jordankooyman/3D-Printed-DIY-Joystick/3D Files/STL/Handle/5-way button spacer.stl

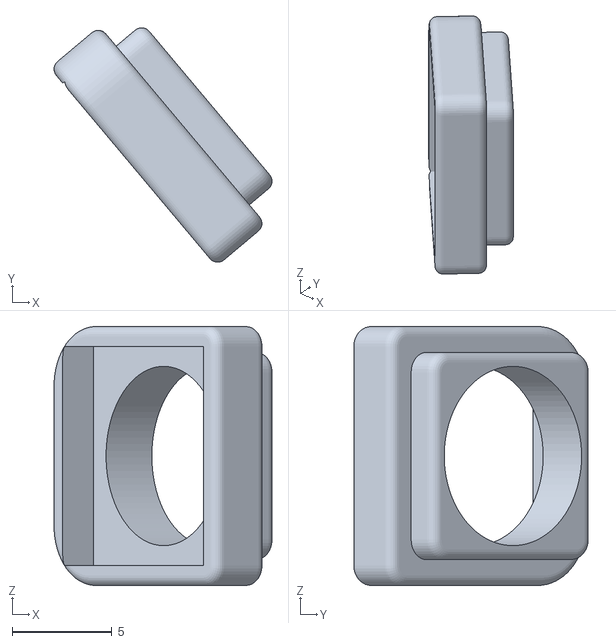
[picture p18: CAD file, 2021-07-30]
3D Files/STL/Handle/5-way button spacer.stl
10.9 x 11.8 x 13.0
