jordankooyman/3D-Printed-DIY-Joystick/3D Files/STL/Throttle Add-On 2.0/Imported Parts - Sample Only/40T 2.75mm MXL Pulley for Pot.stl

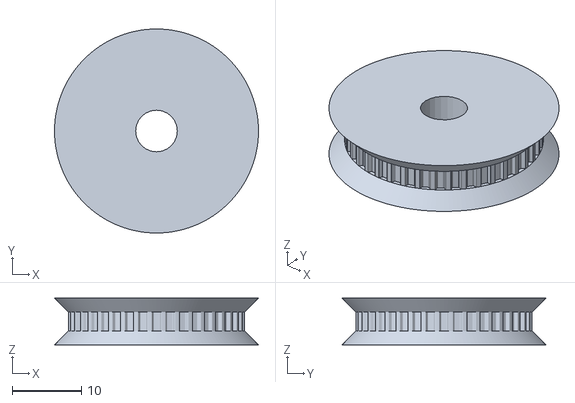
[picture p20: CAD file, 2021-07-30]
3D Files/STL/Throttle Add-On 2.0/Imported Parts - Sample Only/40T 2.75mm MXL Pulley for Pot.stl
29.4 x 29.4 x 6.75
