jordankooyman/3D-Printed-DIY-Joystick/3D Files/STL/Base - Version D/cable cap.stl

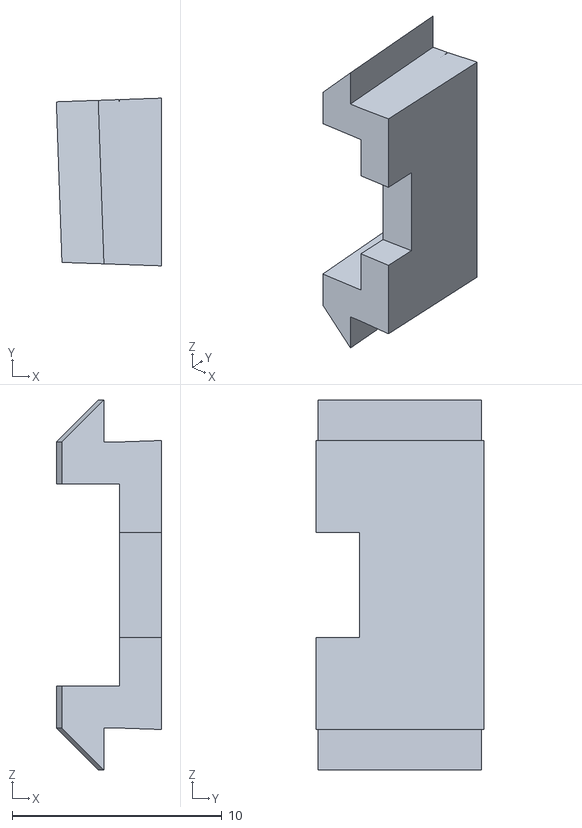
[picture p21: CAD file, 2021-07-30]
3D Files/STL/Base - Version D/cable cap.stl
5.02 x 8.00 x 17.6
