jordankooyman/3D-Printed-DIY-Joystick/3D Files/STL/Chair Mount - For Reference Only/Left Bottom Front Clamp.stl

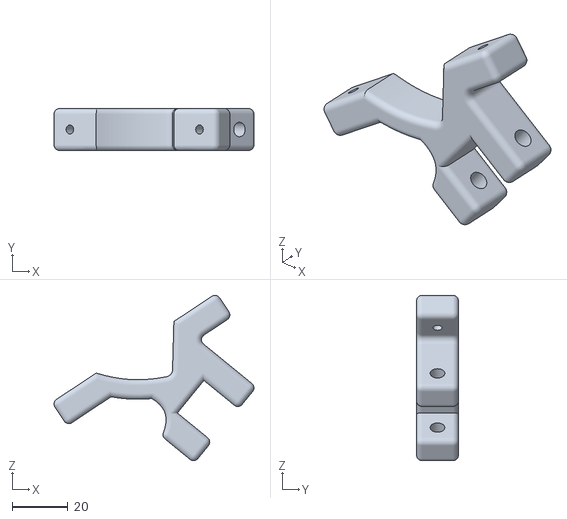
[picture p22: CAD file, 2021-07-30]
3D Files/STL/Chair Mount - For Reference Only/Left Bottom Front Clamp.stl
71.5 x 15.0 x 59.1
