jordankooyman/3D-Printed-DIY-Joystick/3D Files/STL/Handle/Stadium Hat.stl

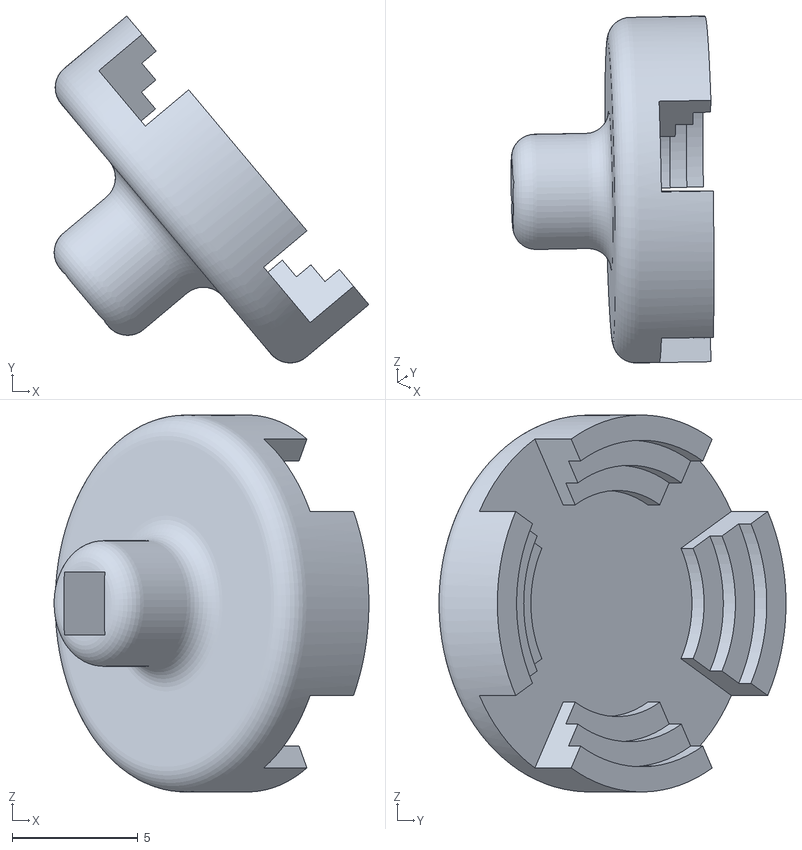
[picture p23: CAD file, 2021-07-30]
3D Files/STL/Handle/Stadium Hat.stl
12.5 x 13.8 x 15.0
