jordankooyman/3D-Printed-DIY-Joystick/3D Files/STL/Throttle Add-On 2.0/Belt Pin Spacer.stl

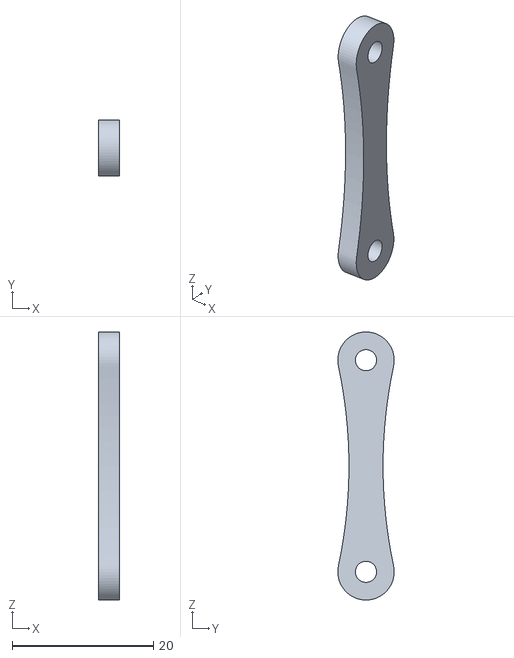
[picture p24: CAD file, 2021-07-30]
3D Files/STL/Throttle Add-On 2.0/Belt Pin Spacer.stl
3.00 x 8.00 x 38.0
