jordankooyman/3D-Printed-DIY-Joystick/3D Files/STL/Throttle Add-On 2.0/Imported Parts - Sample Only/20T 2.75mm MXL Pulley.stl

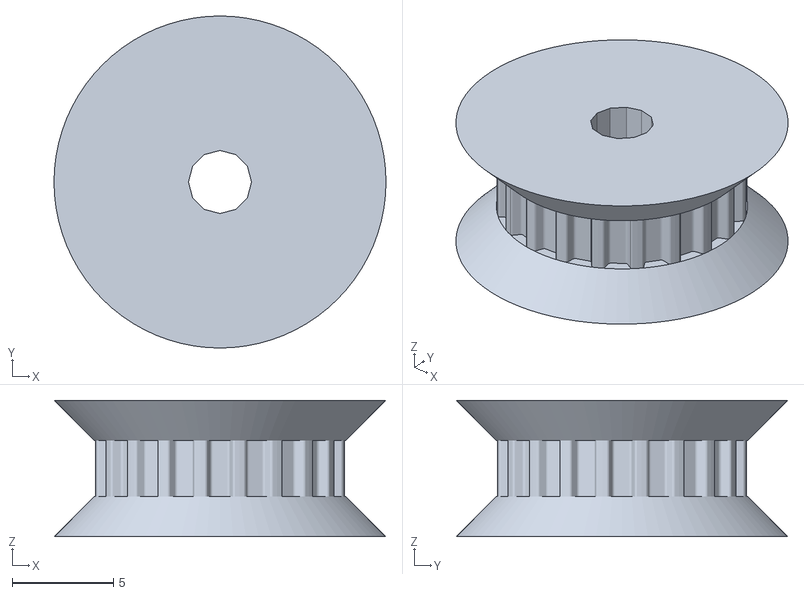
[picture p25: CAD file, 2021-07-30]
3D Files/STL/Throttle Add-On 2.0/Imported Parts - Sample Only/20T 2.75mm MXL Pulley.stl
16.4 x 16.4 x 6.75
