jordankooyman/3D-Printed-DIY-Joystick/3D Files/STL/Base - Version D/Yaw Spring 2.stl

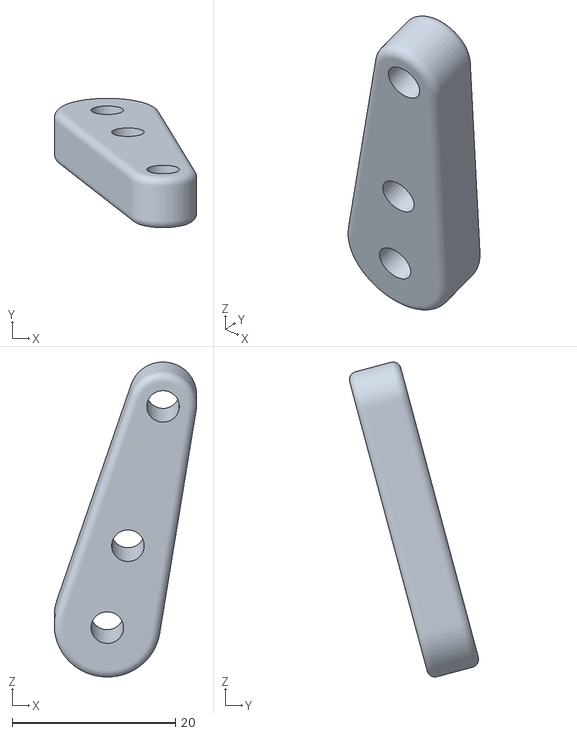
[picture p26: CAD file, 2021-07-30]
3D Files/STL/Base - Version D/Yaw Spring 2.stl
17.4 x 15.8 x 38.6
