jordankooyman/3D-Printed-DIY-Joystick/3D Files/STL/Chair Mount - For Reference Only/Long Support Clamp Base.stl

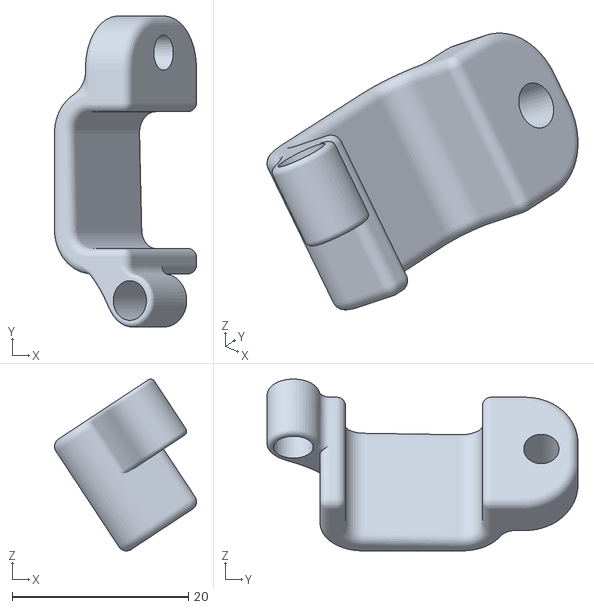
[picture p27: CAD file, 2021-07-30]
3D Files/STL/Chair Mount - For Reference Only/Long Support Clamp Base.stl
16.1 x 35.3 x 19.5
