jordankooyman/3D-Printed-DIY-Joystick/3D Files/STL/Handle/Trim Hat.stl

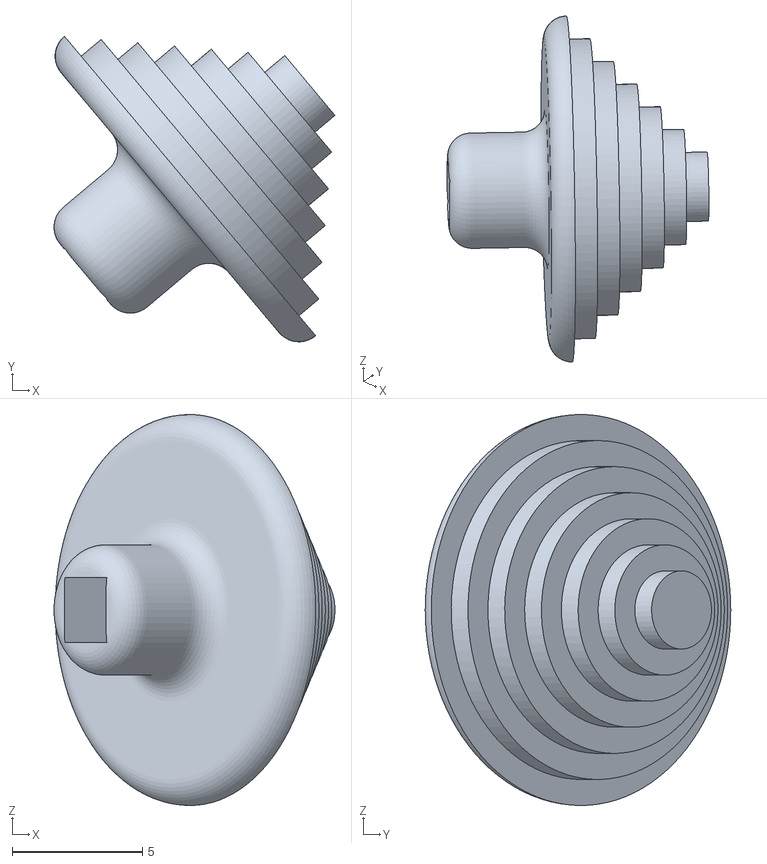
[picture p28: CAD file, 2021-07-30]
3D Files/STL/Handle/Trim Hat.stl
10.8 x 11.7 x 15.0
