jordankooyman/3D-Printed-DIY-Joystick/3D Files/STL/Throttle Add-On 2.0/Cover 2.stl

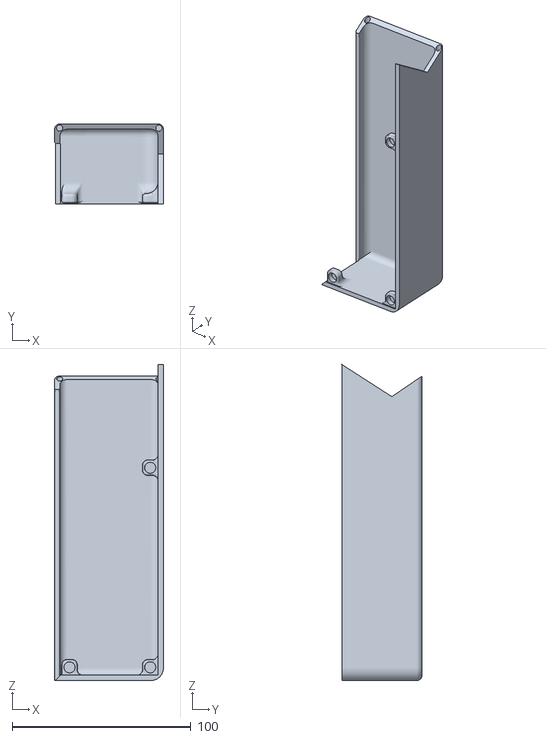
[picture p29: CAD file, 2021-07-30]
3D Files/STL/Throttle Add-On 2.0/Cover 2.stl
61.0 x 45.0 x 177.0
