jordankooyman/3D-Printed-DIY-Joystick/3D Files/STL/Base - Version D/axis_for_ver_D v3.stl

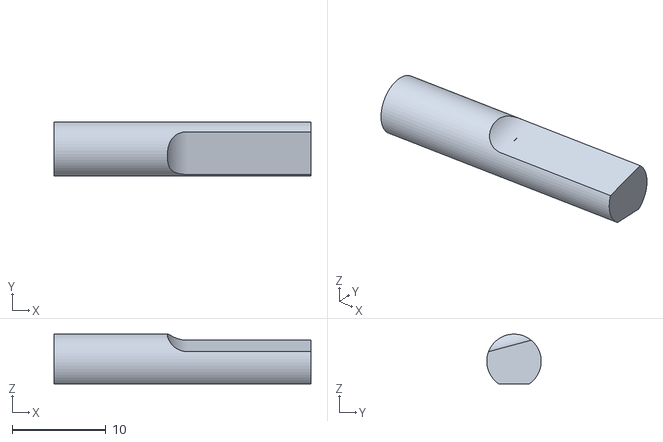
[picture p30: CAD file, 2021-07-30]
3D Files/STL/Base - Version D/axis_for_ver_D v3.stl
27.4 x 5.79 x 5.29
