jordankooyman/3D-Printed-DIY-Joystick/3D Files/STL/Chair Mount - For Reference Only/Long Support Arm Bottom.stl

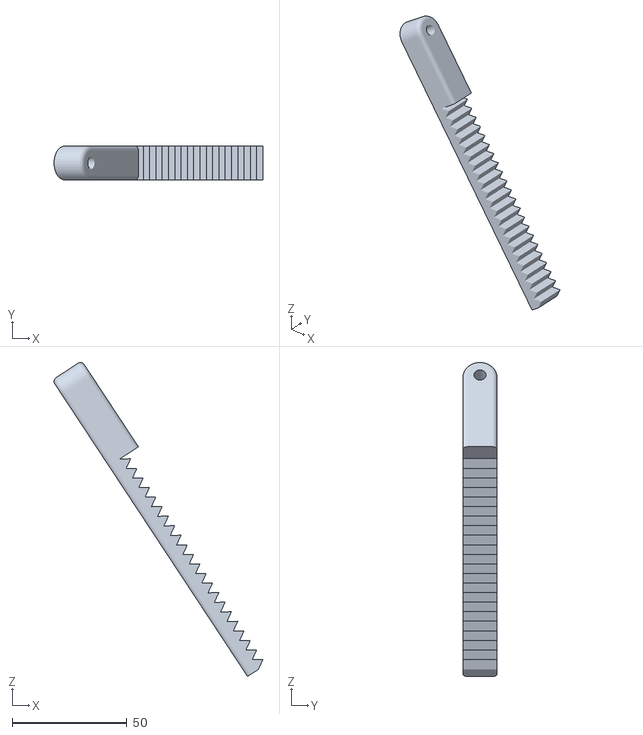
[picture p31: CAD file, 2021-07-30]
3D Files/STL/Chair Mount - For Reference Only/Long Support Arm Bottom.stl
91.2 x 15.0 x 137.1
