jordankooyman/3D-Printed-DIY-Joystick/3D Files/STL/Handle/joystick_grip_right_side v2.stl

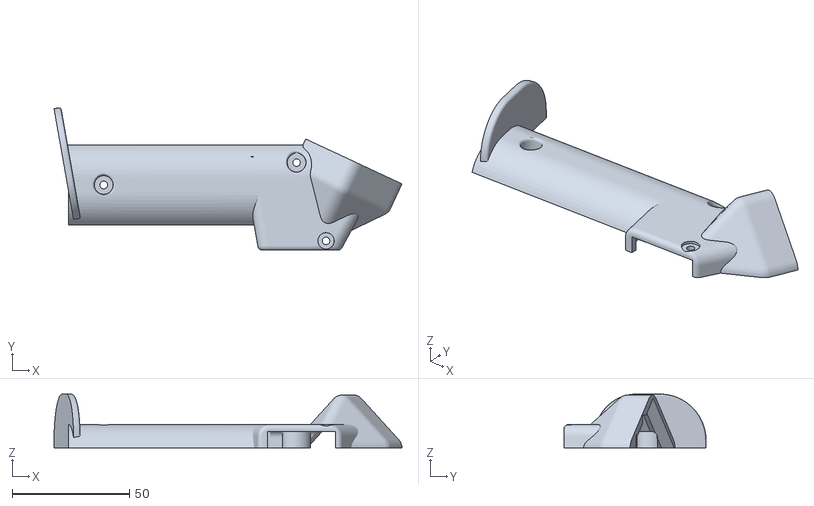
[picture p32: CAD file, 2021-07-30]
3D Files/STL/Handle/joystick_grip_right_side v2.stl
148.5 x 60.8 x 23.0
