jordankooyman/3D-Printed-DIY-Joystick/3D Files/STL/Throttle Add-On 2.0/Mount.stl

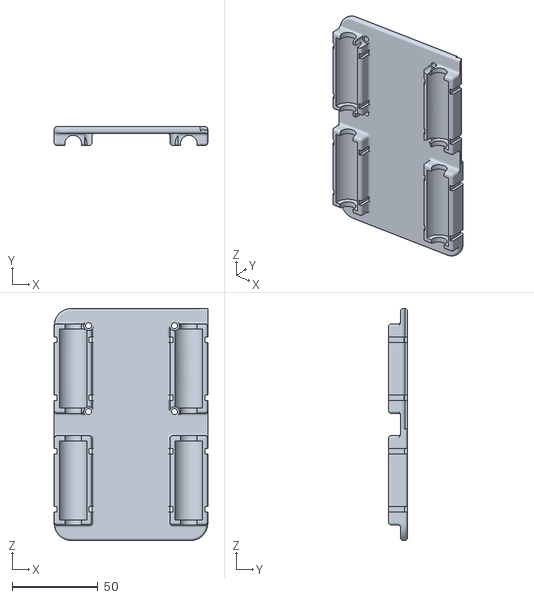
[picture p33: CAD file, 2021-07-30]
3D Files/STL/Throttle Add-On 2.0/Mount.stl
89.4 x 11.0 x 135.0
