jordankooyman/3D-Printed-DIY-Joystick/3D Files/STL/Base - Version D/hinge_cam.stl

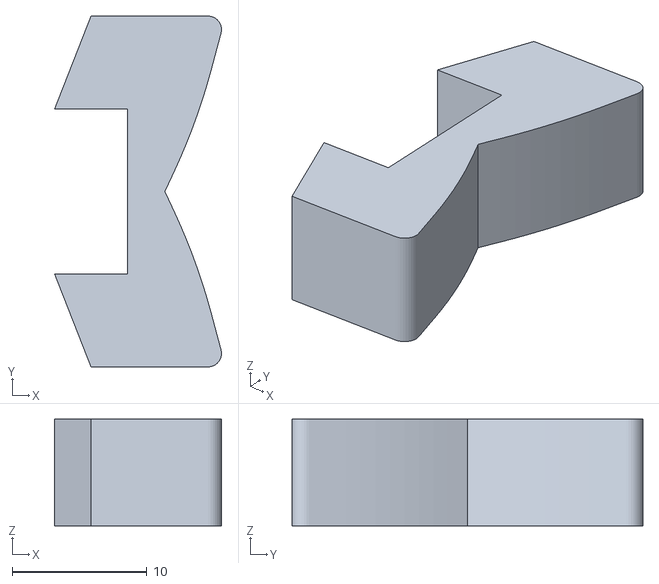
[picture p34: CAD file, 2021-07-30]
3D Files/STL/Base - Version D/hinge_cam.stl
12.4 x 26.0 x 7.90
