jordankooyman/3D-Printed-DIY-Joystick/3D Files/STL/Chair Mount - For Reference Only/Left Top Front Clamp.stl

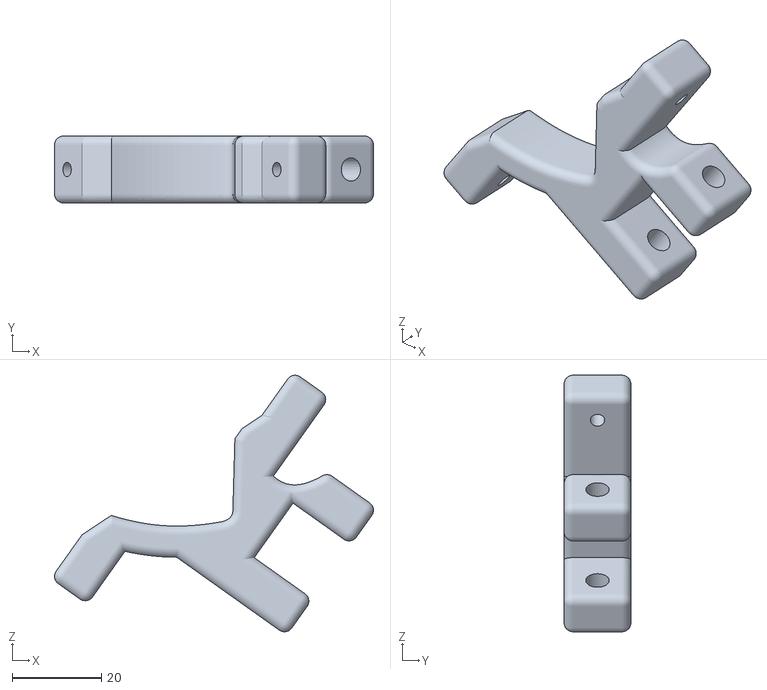
[picture p35: CAD file, 2021-07-30]
3D Files/STL/Chair Mount - For Reference Only/Left Top Front Clamp.stl
71.5 x 15.0 x 57.5
