jordankooyman/3D-Printed-DIY-Joystick/3D Files/STL/Handle/Face Plate.stl

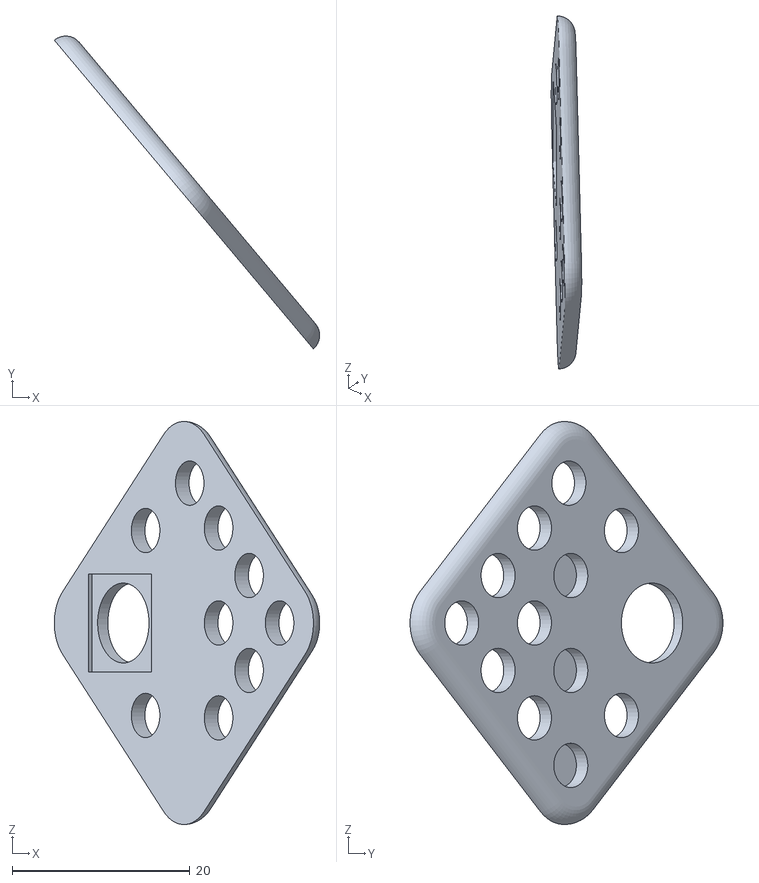
[picture p36: CAD file, 2021-07-30]
3D Files/STL/Handle/Face Plate.stl
29.8 x 35.2 x 45.3
