jordankooyman/3D-Printed-DIY-Joystick/3D Files/STL/Throttle Add-On 2.0/Adjustable Pot Mount.stl

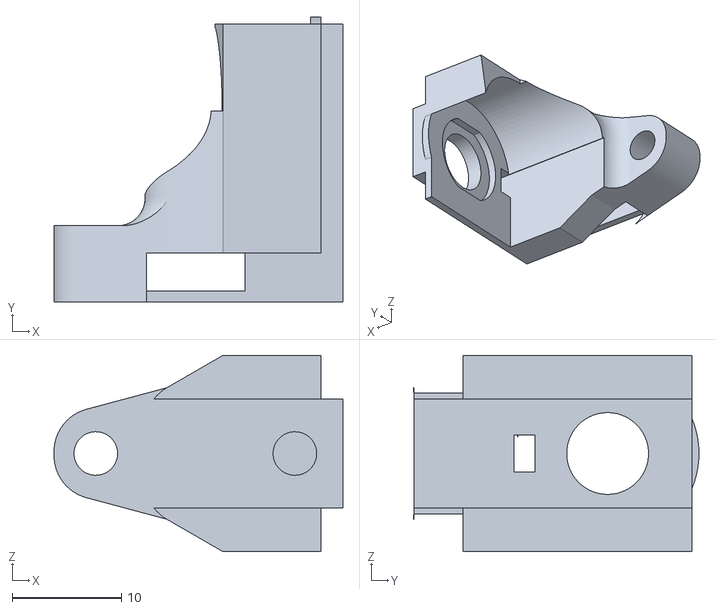
[picture p37: CAD file, 2021-07-30]
3D Files/STL/Throttle Add-On 2.0/Adjustable Pot Mount.stl
26.5 x 26.1 x 18.0
