jordankooyman/3D-Printed-DIY-Joystick/3D Files/STL/Base - Version D/trim knob.stl

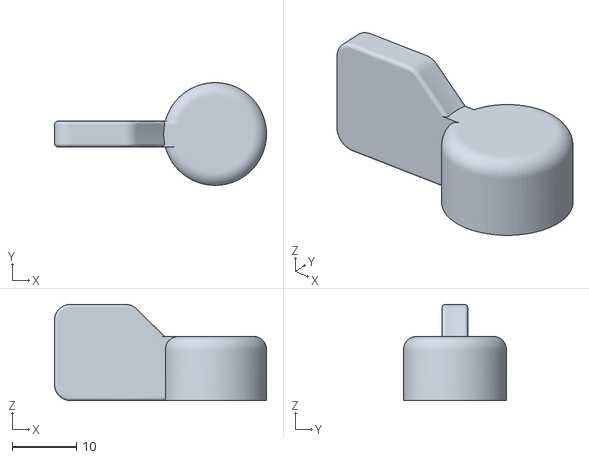
[picture p38: CAD file, 2021-07-30]
3D Files/STL/Base - Version D/trim knob.stl
33.0 x 16.0 x 15.0
