jordankooyman/3D-Printed-DIY-Joystick/3D Files/STL/Chair Mount - For Reference Only/Short Support Arm 2.stl

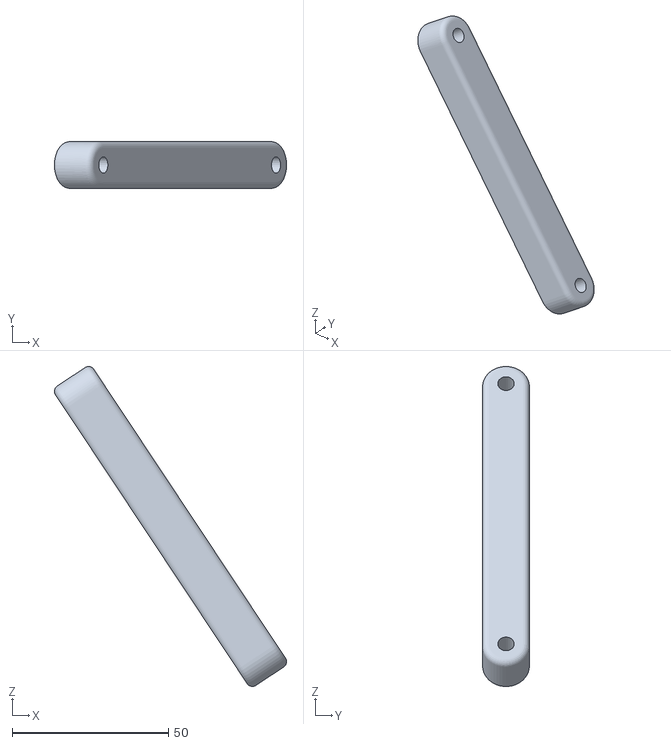
[picture p39: CAD file, 2021-07-30]
3D Files/STL/Chair Mount - For Reference Only/Short Support Arm 2.stl
74.3 x 15.0 x 102.4
