jordankooyman/3D-Printed-DIY-Joystick/3D Files/STL/Handle/joystick grip left side filled.3mf

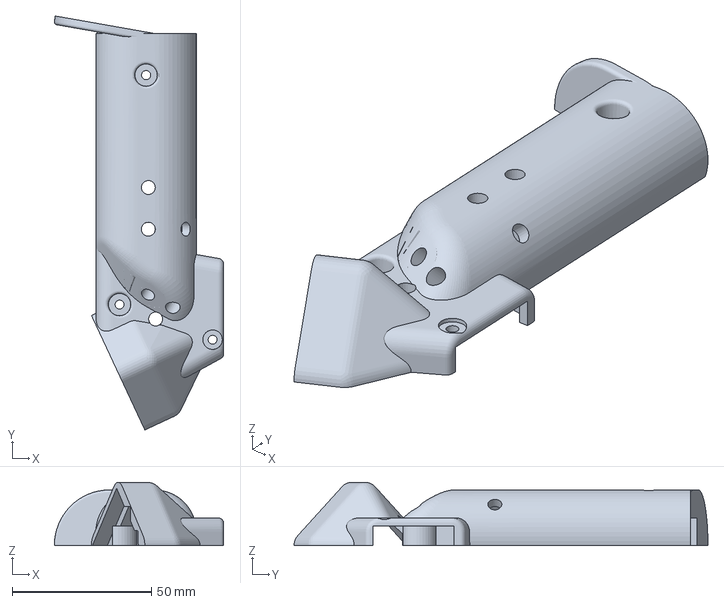
[picture p40: CAD file, 2021-07-30]
3D Files/STL/Handle/joystick grip left side filled.3mf
60.8 x 148.5 x 22.7 mm
