jordankooyman/3D-Printed-DIY-Joystick/3D Files/STL/Throttle Add-On 2.0/Mount Side.stl

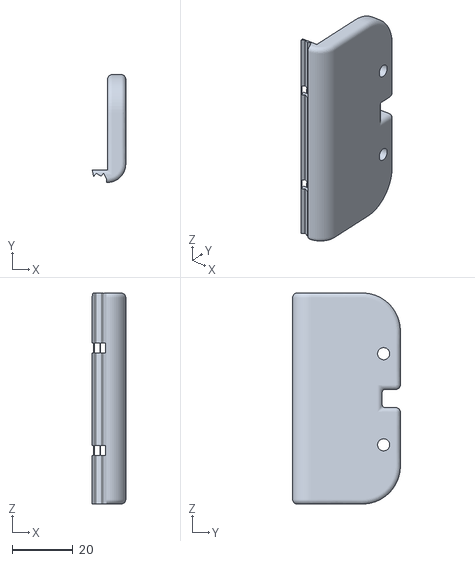
[picture p41: CAD file, 2021-07-30]
3D Files/STL/Throttle Add-On 2.0/Mount Side.stl
11.1 x 35.5 x 69.5
