jordankooyman/3D-Printed-DIY-Joystick/3D Files/STL/Base - Version D/Wire Storage Clip.stl

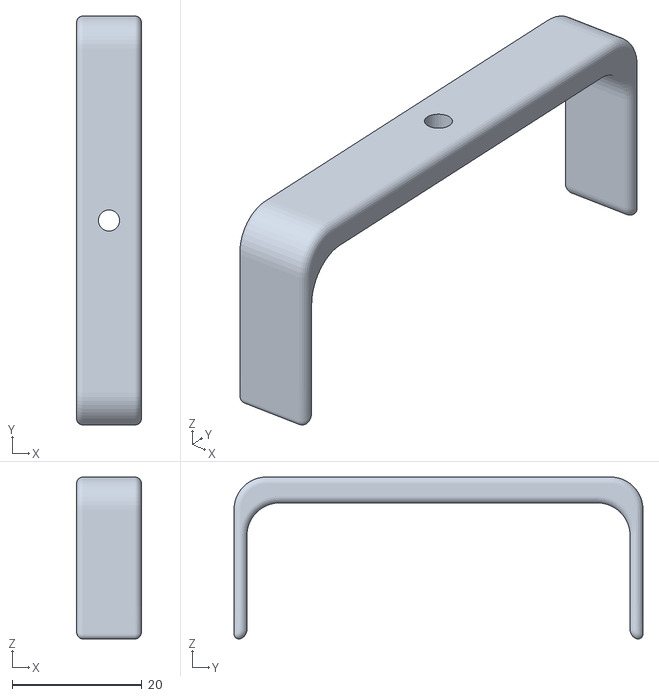
[picture p42: CAD file, 2021-07-30]
3D Files/STL/Base - Version D/Wire Storage Clip.stl
10.0 x 63.0 x 25.0
