jordankooyman/3D-Printed-DIY-Joystick/3D Files/STL/Chair Mount - For Reference Only/Left Clamp Back Bottom.stl

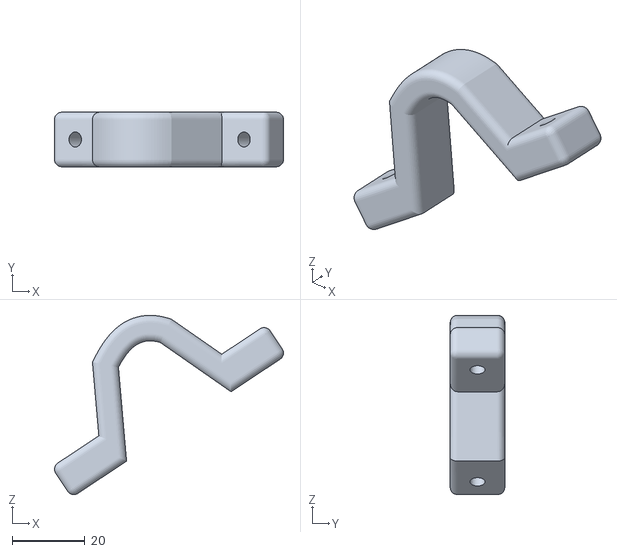
[picture p43: CAD file, 2021-07-30]
3D Files/STL/Chair Mount - For Reference Only/Left Clamp Back Bottom.stl
62.9 x 15.0 x 49.2
