jordankooyman/3D-Printed-DIY-Joystick/3D Files/STL/Handle/trigger.stl

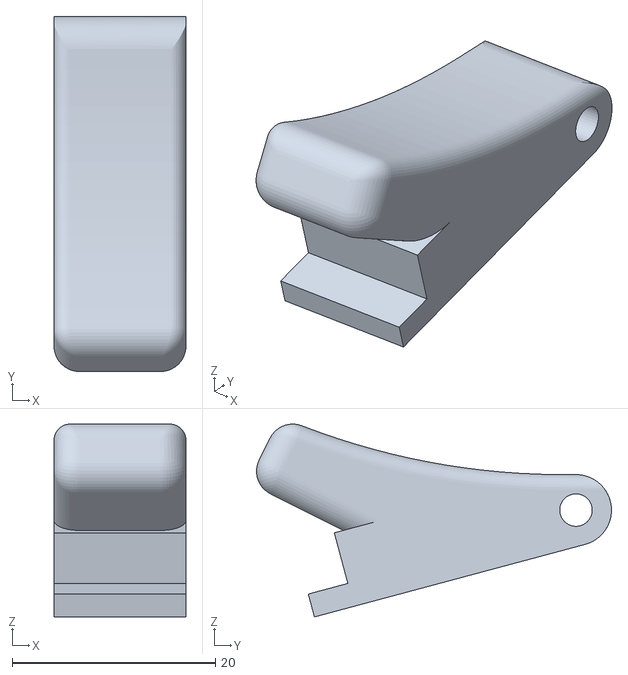
[picture p44: CAD file, 2021-07-30]
3D Files/STL/Handle/trigger.stl
13.0 x 35.0 x 19.0
