jordankooyman/3D-Printed-DIY-Joystick/3D Files/STL/Throttle Add-On 2.0/Base 2.stl

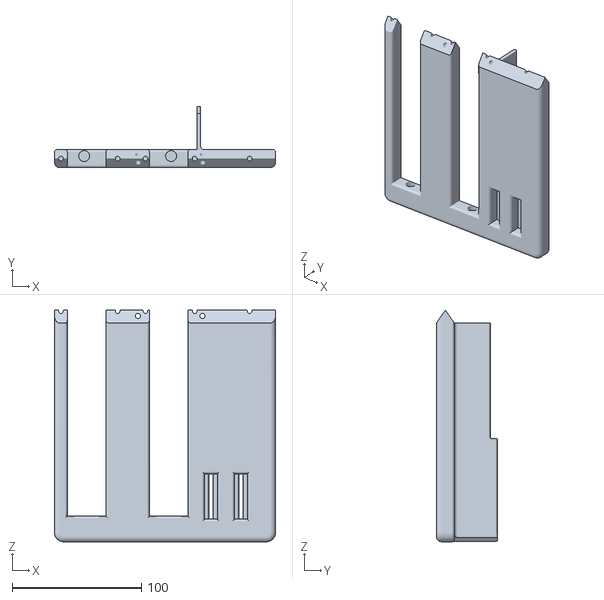
[picture p45: CAD file, 2021-07-30]
3D Files/STL/Throttle Add-On 2.0/Base 2.stl
171.2 x 47.5 x 179.5
