jordankooyman/3D-Printed-DIY-Joystick/3D Files/STL/Base - Version D/base_cover.stl

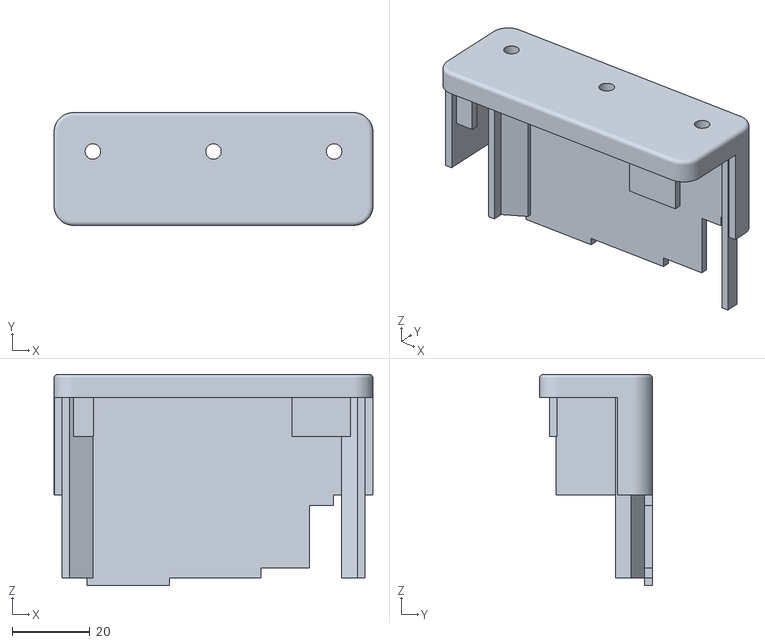
[picture p46: CAD file, 2021-07-30]
3D Files/STL/Base - Version D/base_cover.stl
82.0 x 29.0 x 54.3
