jordankooyman/3D-Printed-DIY-Joystick/3D Files/STL/Chair Mount - For Reference Only/M5 Cap.stl

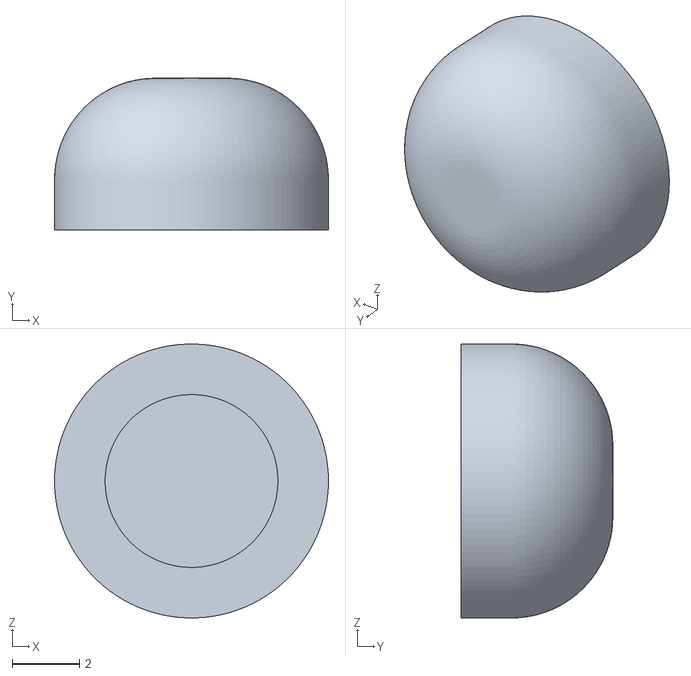
[picture p47: CAD file, 2021-07-30]
3D Files/STL/Chair Mount - For Reference Only/M5 Cap.stl
8.12 x 4.50 x 8.12
