jordankooyman/3D-Printed-DIY-Joystick/3D Files/STL/Handle/joystick_grip_left_side v2.stl

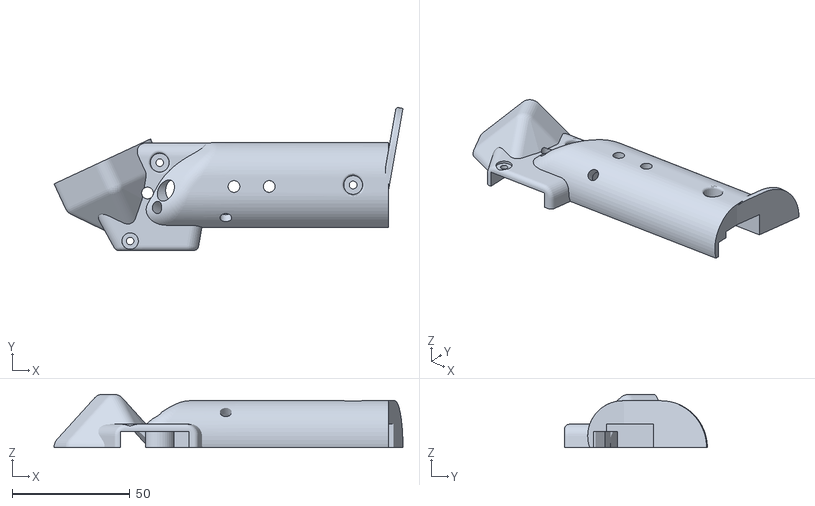
[picture p48: CAD file, 2021-07-30]
3D Files/STL/Handle/joystick_grip_left_side v2.stl
148.5 x 60.8 x 22.7
