jordankooyman/3D-Printed-DIY-Joystick/3D Files/STL/Base - Version D/M4 Bearing Spacer.stl

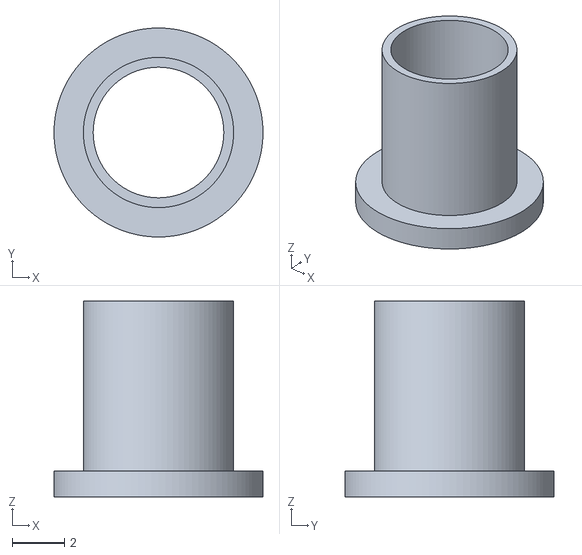
[picture p50: CAD file, 2021-07-30]
3D Files/STL/Base - Version D/M4 Bearing Spacer.stl
8.00 x 8.00 x 7.50
