jordankooyman/3D-Printed-DIY-Joystick/3D Files/STL/Handle/Button Cap Body.stl

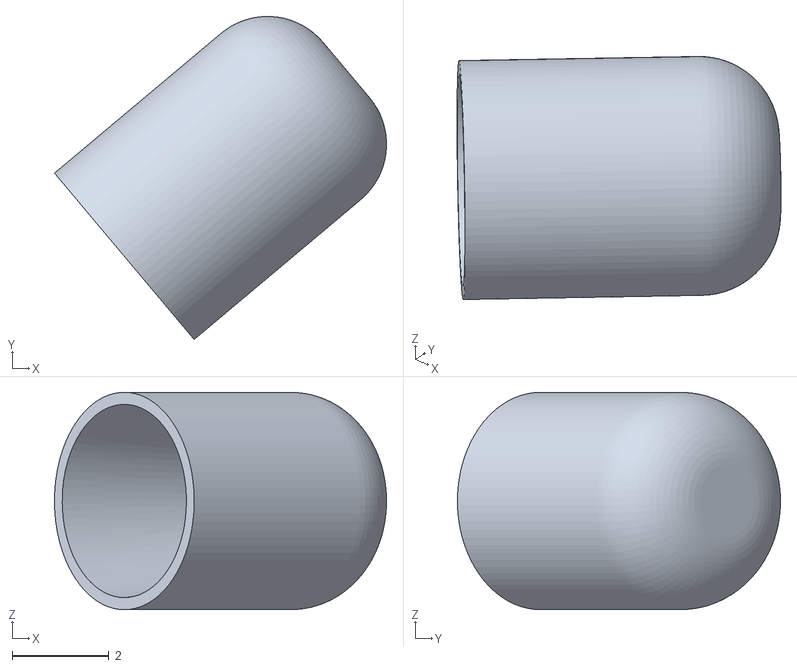
[picture p51: CAD file, 2021-07-30]
3D Files/STL/Handle/Button Cap Body.stl
6.87 x 6.69 x 4.50
