jordankooyman/3D-Printed-DIY-Joystick/3D Files/STL/Throttle Add-On 2.0/Idler Axle.stl

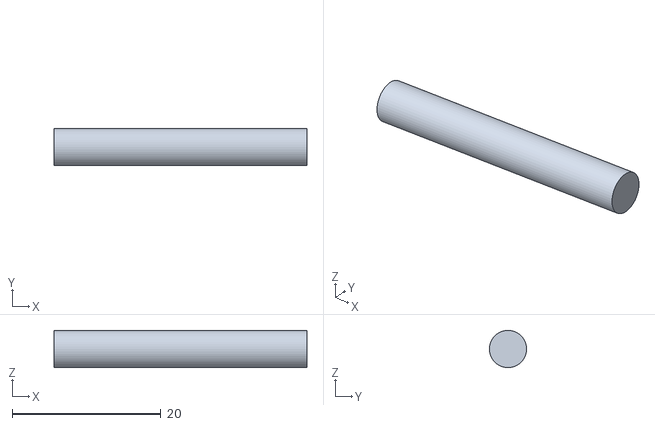
[picture p52: CAD file, 2021-07-30]
3D Files/STL/Throttle Add-On 2.0/Idler Axle.stl
34.0 x 5.00 x 5.00
