jordankooyman/3D-Printed-DIY-Joystick/3D Files/STL/Base - Version D/Bottom.stl

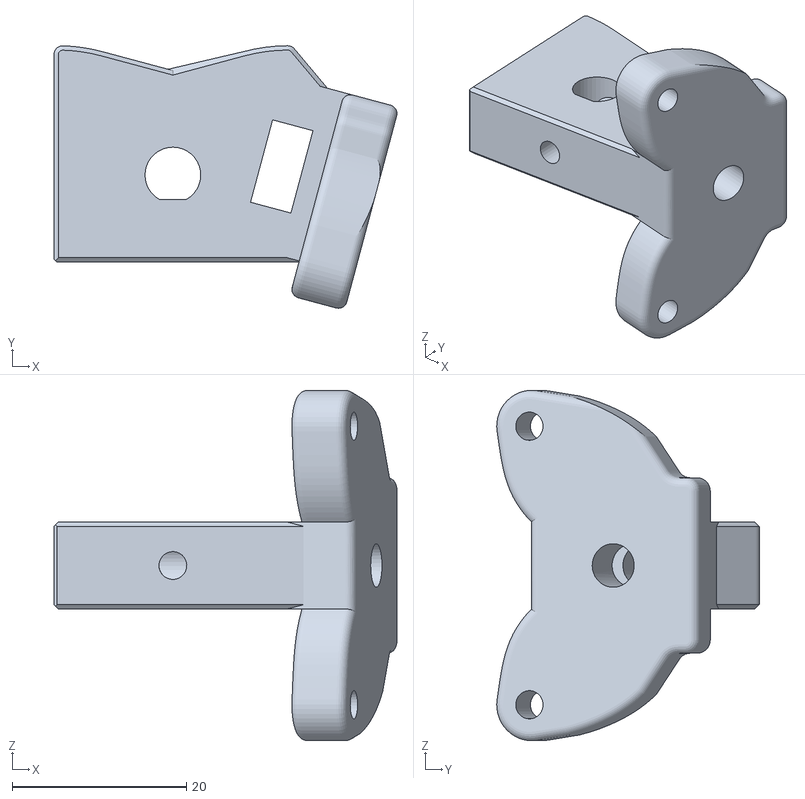
[picture p53: CAD file, 2021-07-30]
3D Files/STL/Base - Version D/Bottom.stl
39.4 x 30.2 x 40.2
