jordankooyman/3D-Printed-DIY-Joystick/3D Files/STL/Chair Mount - For Reference Only/Right Clamp Back Bottom.stl

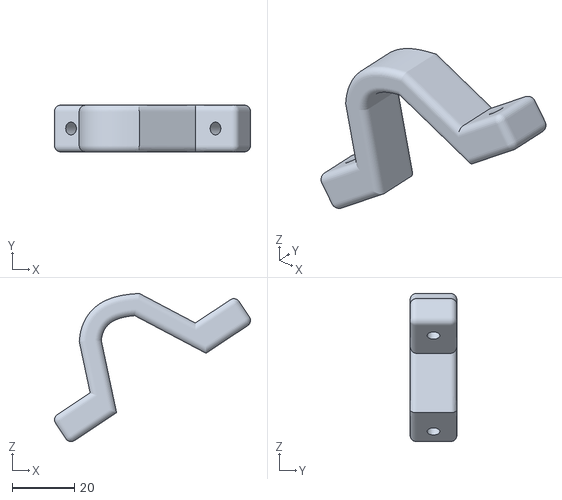
[picture p54: CAD file, 2021-07-30]
3D Files/STL/Chair Mount - For Reference Only/Right Clamp Back Bottom.stl
62.9 x 15.0 x 47.5
