jordankooyman/3D-Printed-DIY-Joystick/3D Files/STL/Base - Version D/cam_arm.stl

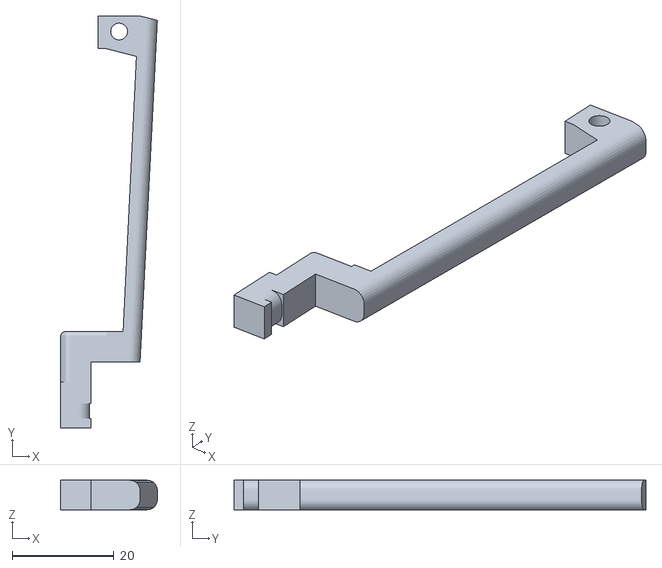
[picture p55: CAD file, 2021-07-30]
3D Files/STL/Base - Version D/cam_arm.stl
19.0 x 81.0 x 5.80
