jordankooyman/3D-Printed-DIY-Joystick/3D Files/STL/Chair Mount - For Reference Only/Short Support Arm.stl

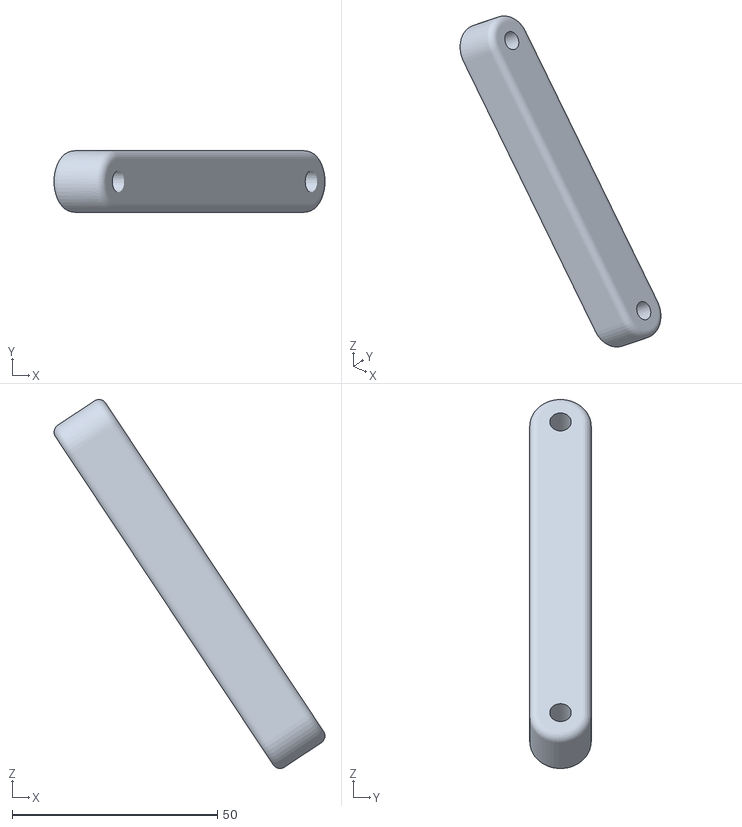
[picture p56: CAD file, 2021-07-30]
3D Files/STL/Chair Mount - For Reference Only/Short Support Arm.stl
66.0 x 15.0 x 89.9
