jordankooyman/3D-Printed-DIY-Joystick/3D Files/STL/Base - Version D/Mount Base.stl

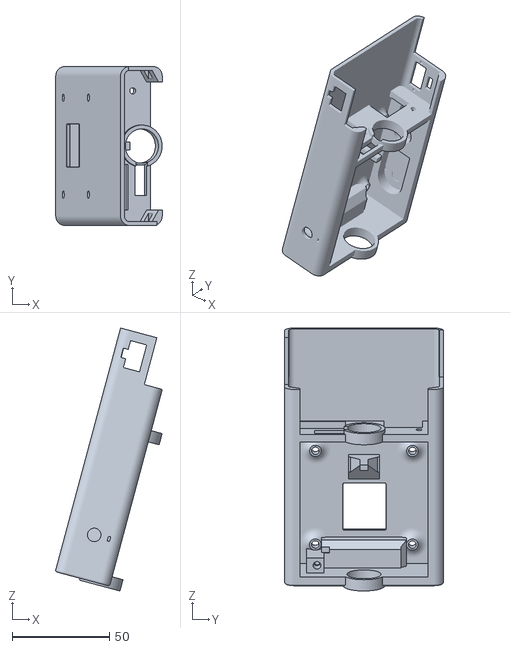
[picture p57: CAD file, 2021-07-30]
3D Files/STL/Base - Version D/Mount Base.stl
55.0 x 82.0 x 135.5
