jordankooyman/3D-Printed-DIY-Joystick/3D Files/STL/Chair Mount - For Reference Only/Right Bottom Front Clamp.stl

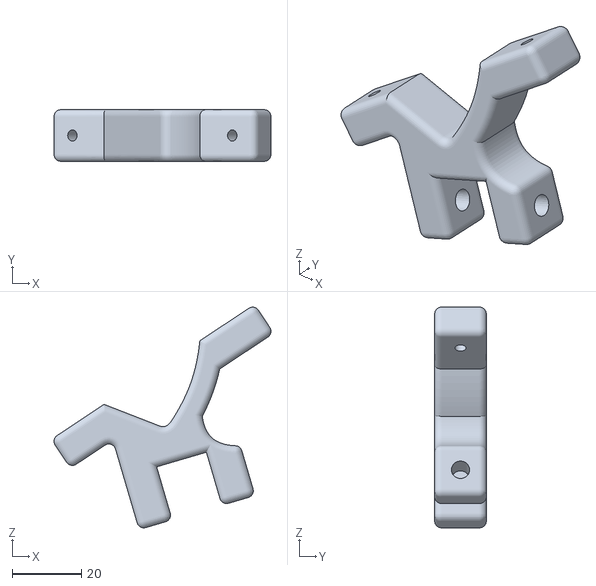
[picture p58: CAD file, 2021-07-30]
3D Files/STL/Chair Mount - For Reference Only/Right Bottom Front Clamp.stl
62.9 x 15.0 x 63.9
