jordankooyman/3D-Printed-DIY-Joystick/3D Files/STL/Base - Version D/Top.stl

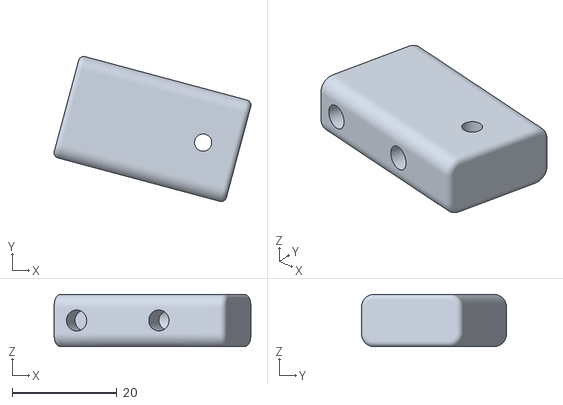
[picture p59: CAD file, 2021-07-30]
3D Files/STL/Base - Version D/Top.stl
37.6 x 27.7 x 10.0
