jordankooyman/3D-Printed-DIY-Joystick/3D Files/STL/Chair Mount - For Reference Only/Base Mount Top.stl

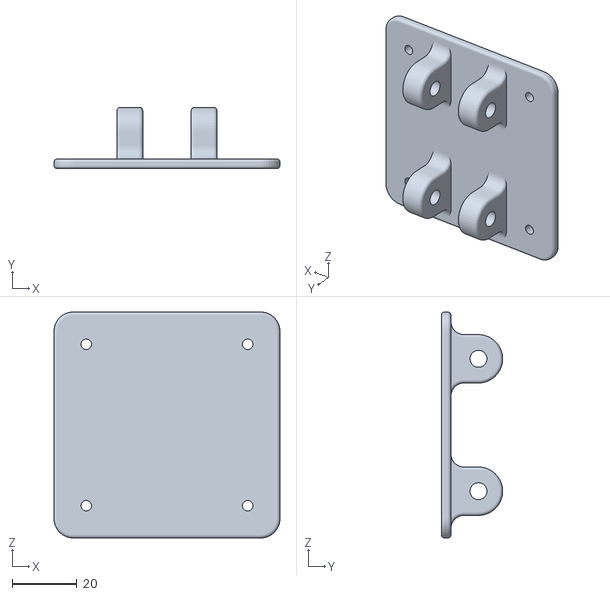
[picture p60: CAD file, 2021-07-30]
3D Files/STL/Chair Mount - For Reference Only/Base Mount Top.stl
70.0 x 19.0 x 70.0
