jordankooyman/3D-Printed-DIY-Joystick/3D Files/STL/Base - Version D/hinge_cam_slider_for_ver_C v3.stl

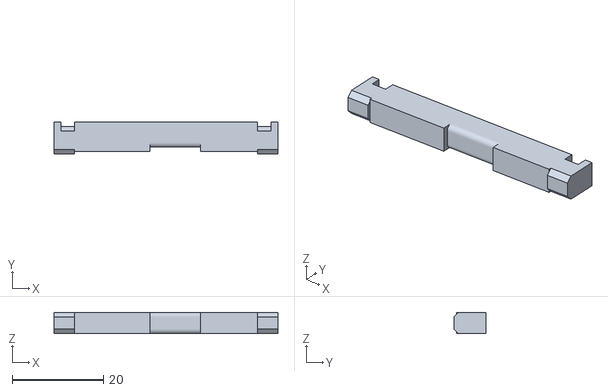
[picture p61: CAD file, 2021-07-30]
3D Files/STL/Base - Version D/hinge_cam_slider_for_ver_C v3.stl
49.0 x 7.00 x 4.70
