jordankooyman/3D-Printed-DIY-Joystick/3D Files/STL/Chair Mount - For Reference Only/M3 Cap.stl

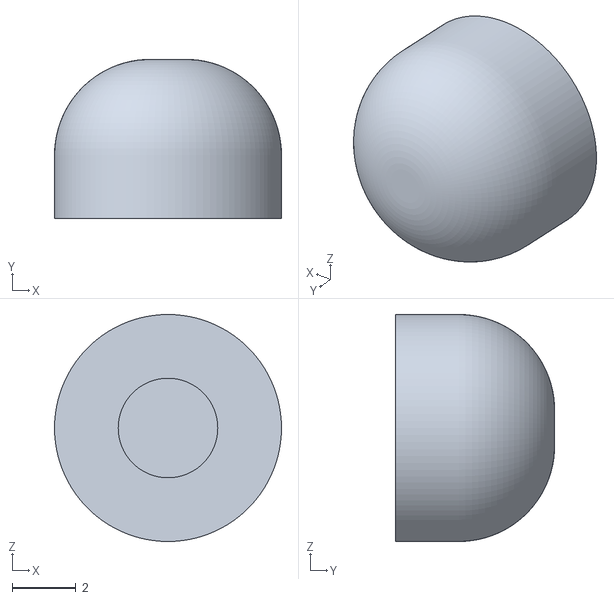
[picture p62: CAD file, 2021-07-30]
3D Files/STL/Chair Mount - For Reference Only/M3 Cap.stl
7.12 x 5.00 x 7.13
