jordankooyman/3D-Printed-DIY-Joystick/3D Files/STL/Base - Version D/hinge_ver_D_-_606_bearings v3.stl

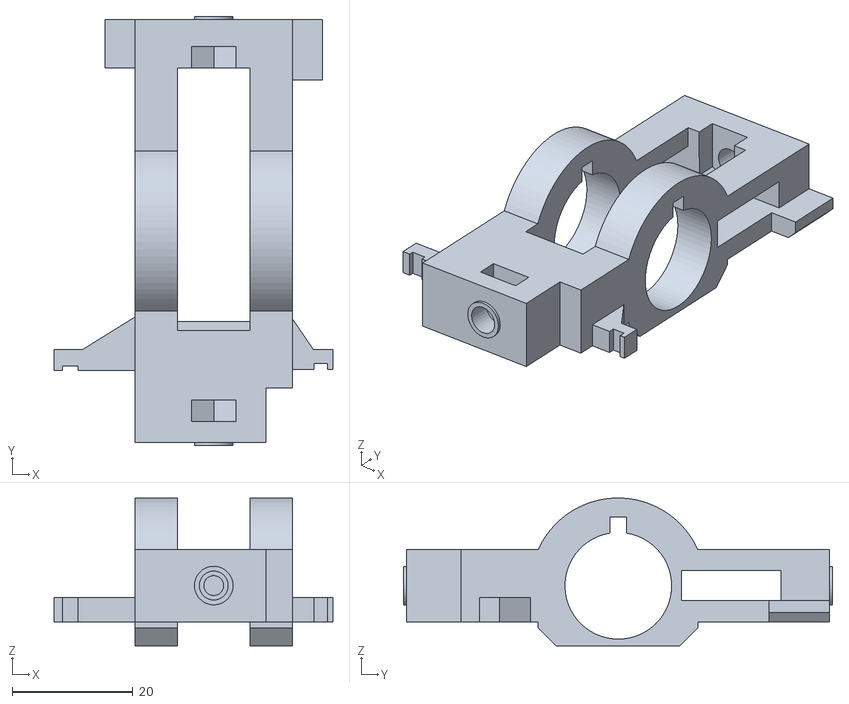
[picture p63: CAD file, 2021-07-30]
3D Files/STL/Base - Version D/hinge_ver_D_-_606_bearings v3.stl
46.1 x 71.0 x 24.5
