jordankooyman/3D-Printed-DIY-Joystick/3D Files/STL/Chair Mount - For Reference Only/Right Clamp Back Top.stl

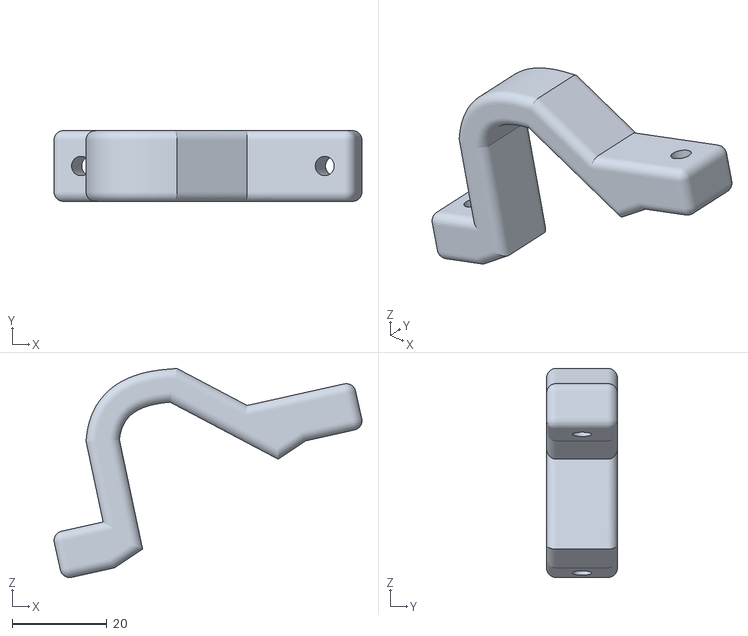
[picture p64: CAD file, 2021-07-30]
3D Files/STL/Chair Mount - For Reference Only/Right Clamp Back Top.stl
65.2 x 15.0 x 44.3
