jordankooyman/3D-Printed-DIY-Joystick/Images/Pictures From Build Guide Video/Untitled_2.1.8.jpg

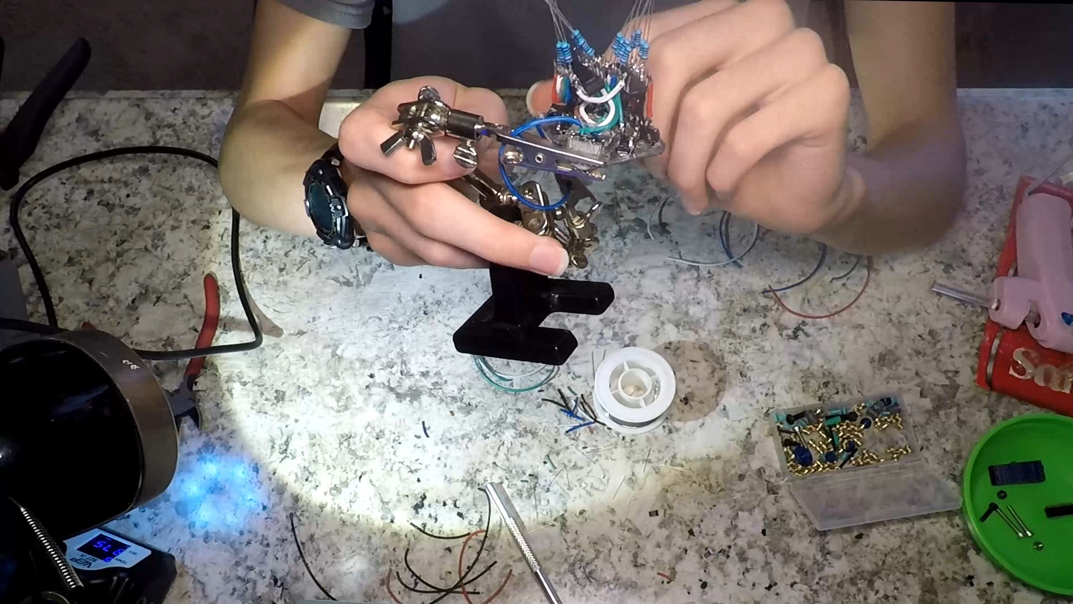
Images/Pictures From Build Guide Video/Untitled_2.1.8.jpg
