jordankooyman/3D-Printed-DIY-Joystick/Images/Pictures From Build Guide Video/Untitled_2.1.18.jpg

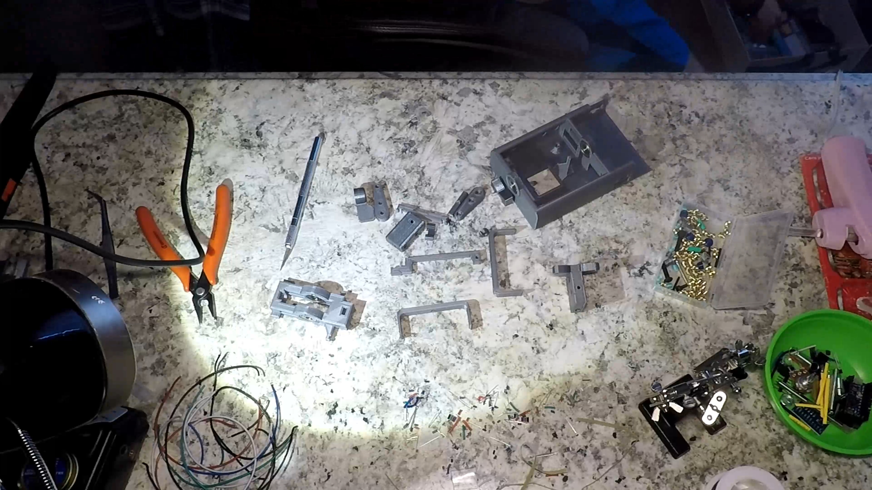
Images/Pictures From Build Guide Video/Untitled_2.1.18.jpg
