jordankooyman/3D-Printed-DIY-Joystick/Images/Final Result/GOPR8978.JPG

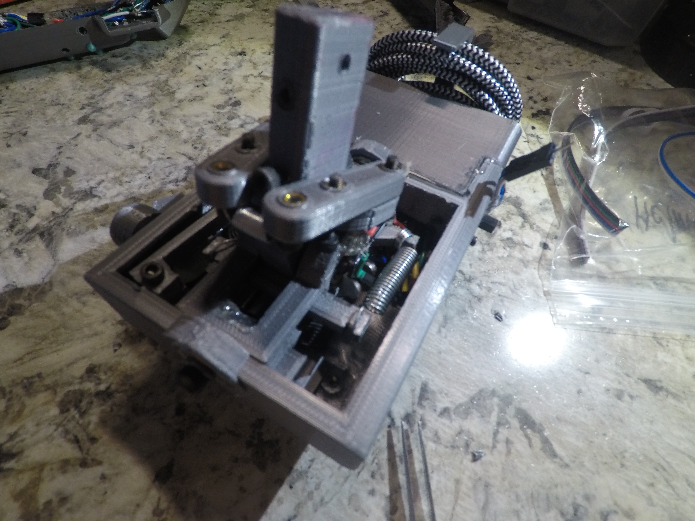
Images/Final Result/GOPR8978.JPG
