jordankooyman/3D-Printed-DIY-Joystick/Images/Final Result/GOPR8979.JPG

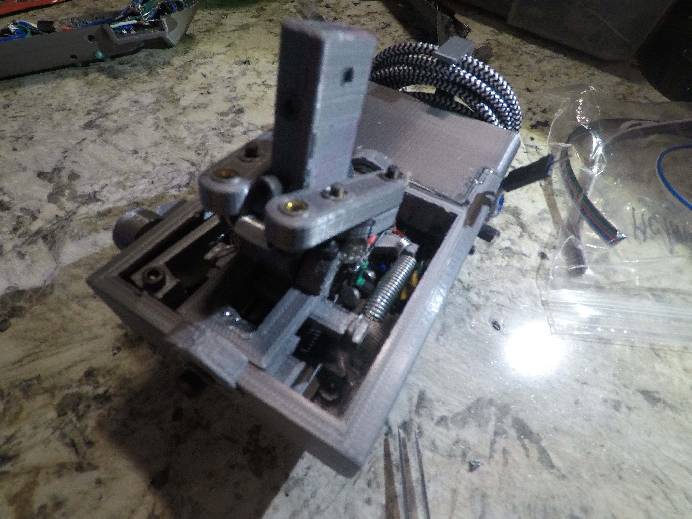
Images/Final Result/GOPR8979.JPG
