jordankooyman/3D-Printed-DIY-Joystick/Images/Final Result/GOPR8980.JPG

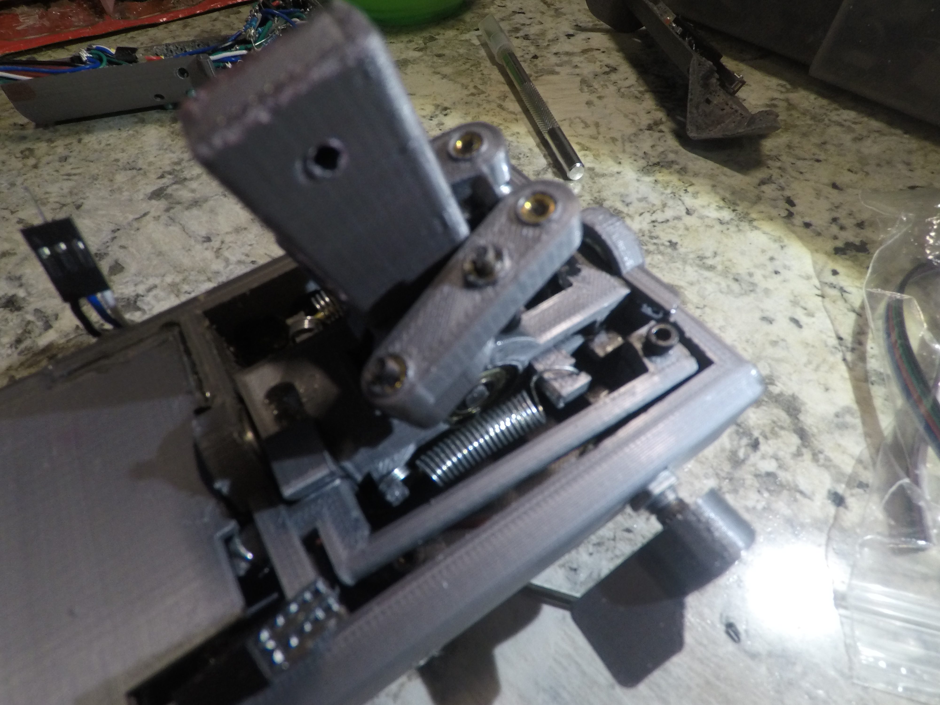
Images/Final Result/GOPR8980.JPG
