jordankooyman/3D-Printed-DIY-Joystick/Images/Final Result/GOPR8981.JPG

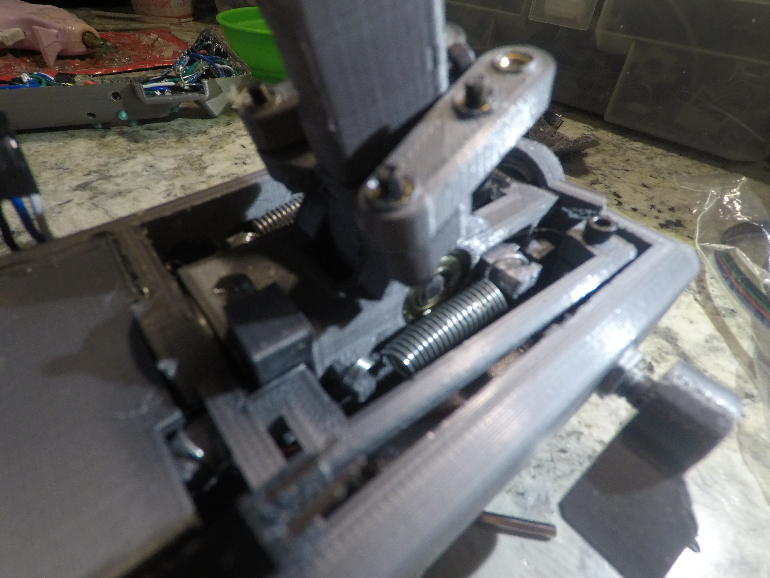
Images/Final Result/GOPR8981.JPG
