jordankooyman/3D-Printed-DIY-Joystick/Images/Final Result/GOPR8982.JPG

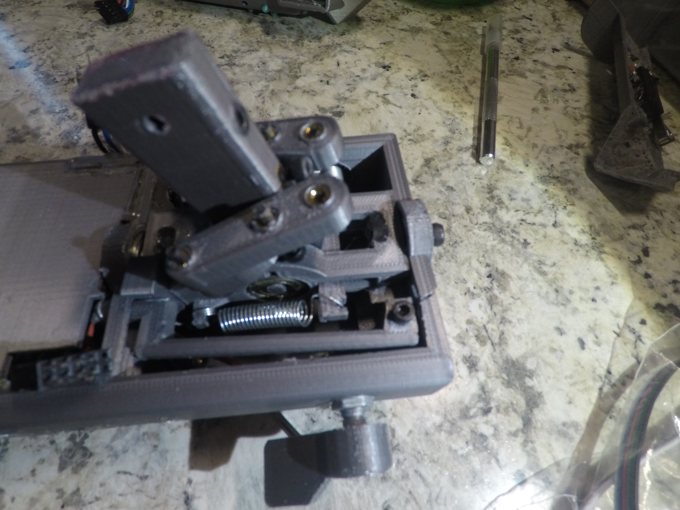
Images/Final Result/GOPR8982.JPG
