jordankooyman/3D-Printed-DIY-Joystick/Images/Final Result/GOPR8983.JPG

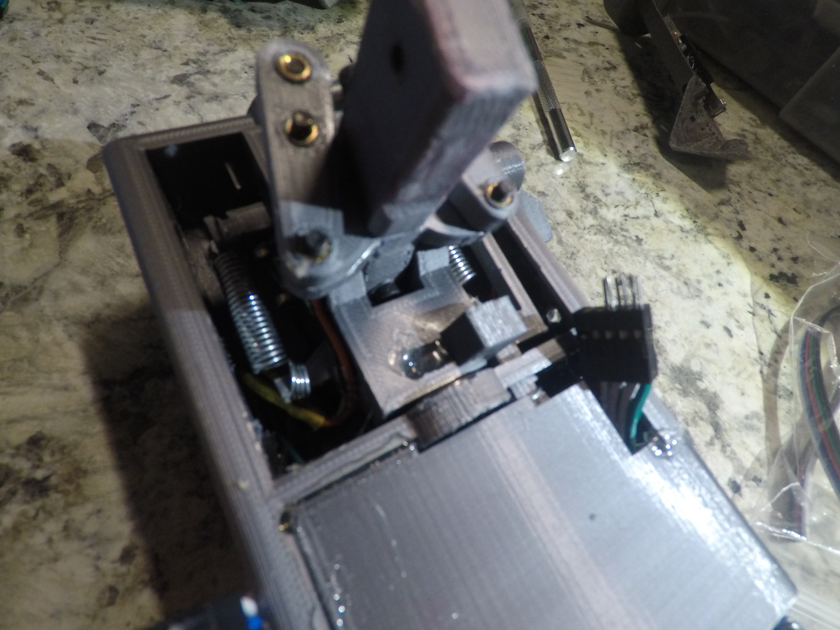
Images/Final Result/GOPR8983.JPG
