jordankooyman/3D-Printed-DIY-Joystick/Images/Final Result/GOPR8984.JPG

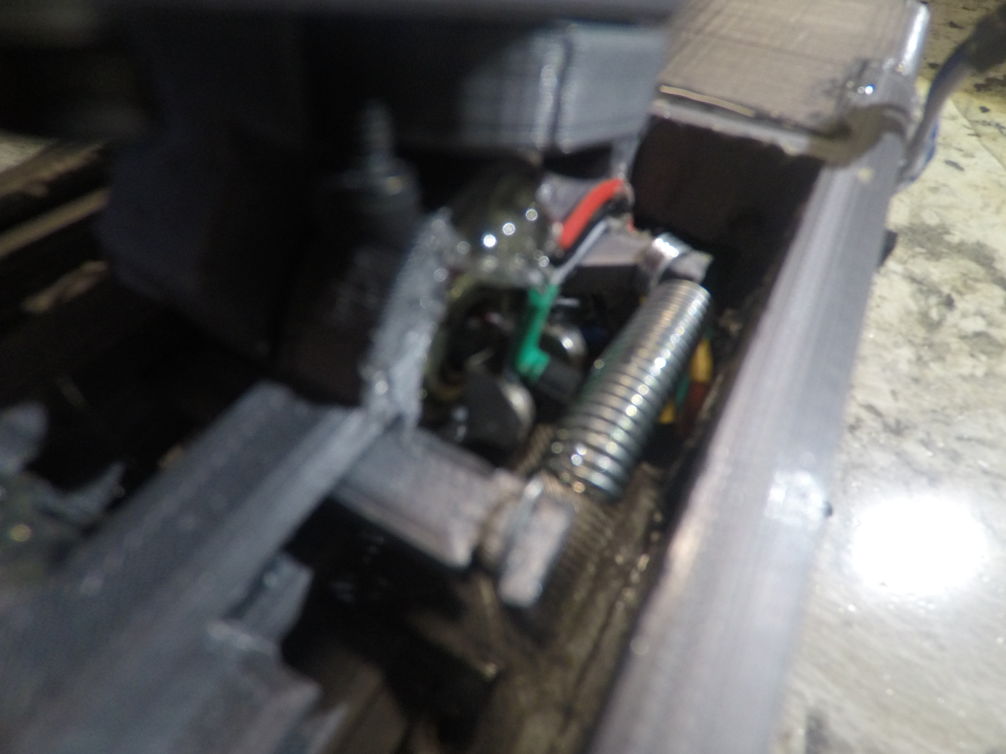
Images/Final Result/GOPR8984.JPG
