jordankooyman/3D-Printed-DIY-Joystick/Images/Final Result/GOPR8985.JPG

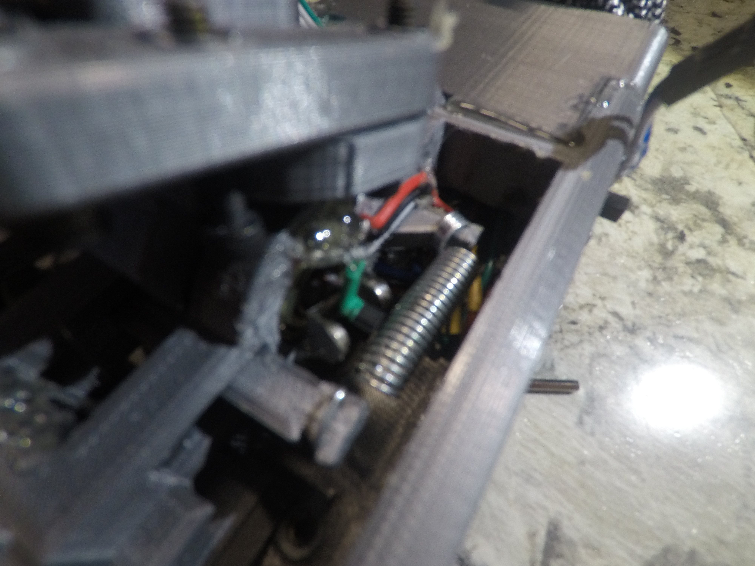
Images/Final Result/GOPR8985.JPG
