jordankooyman/3D-Printed-DIY-Joystick/Images/Final Result/GOPR8986.JPG

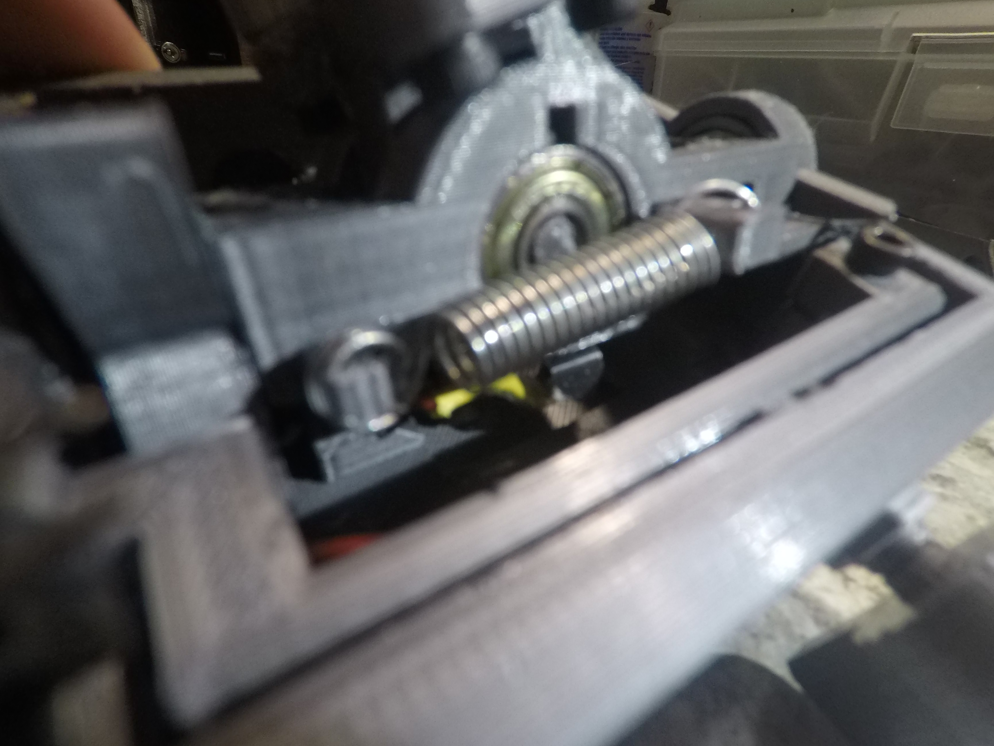
Images/Final Result/GOPR8986.JPG
