jordankooyman/3D-Printed-DIY-Joystick/Images/Final Result/GOPR8989.JPG

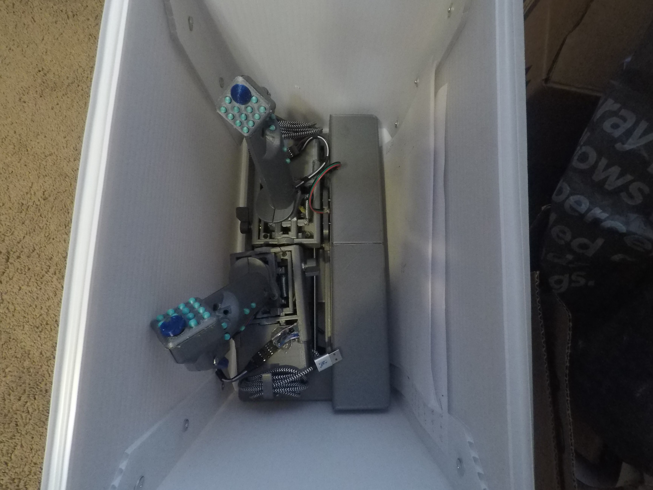
Images/Final Result/GOPR8989.JPG
