jordankooyman/3D-Printed-DIY-Joystick/Images/Final Result/Throttle Joystick Front View.png

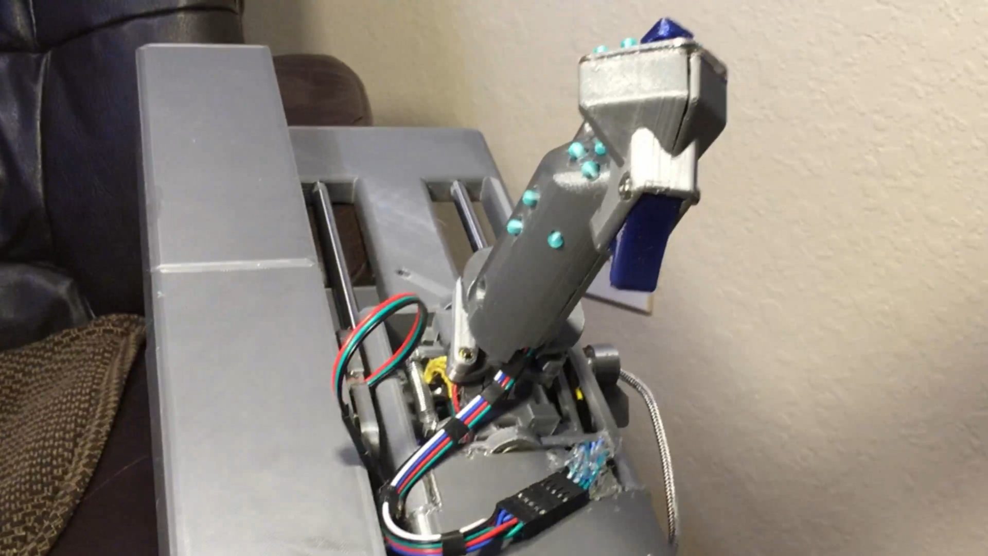
Images/Final Result/Throttle Joystick Front View.png
