jordankooyman/3D-Printed-DIY-Joystick/Images/Final Result/Throttle Joystick Side Videw.png

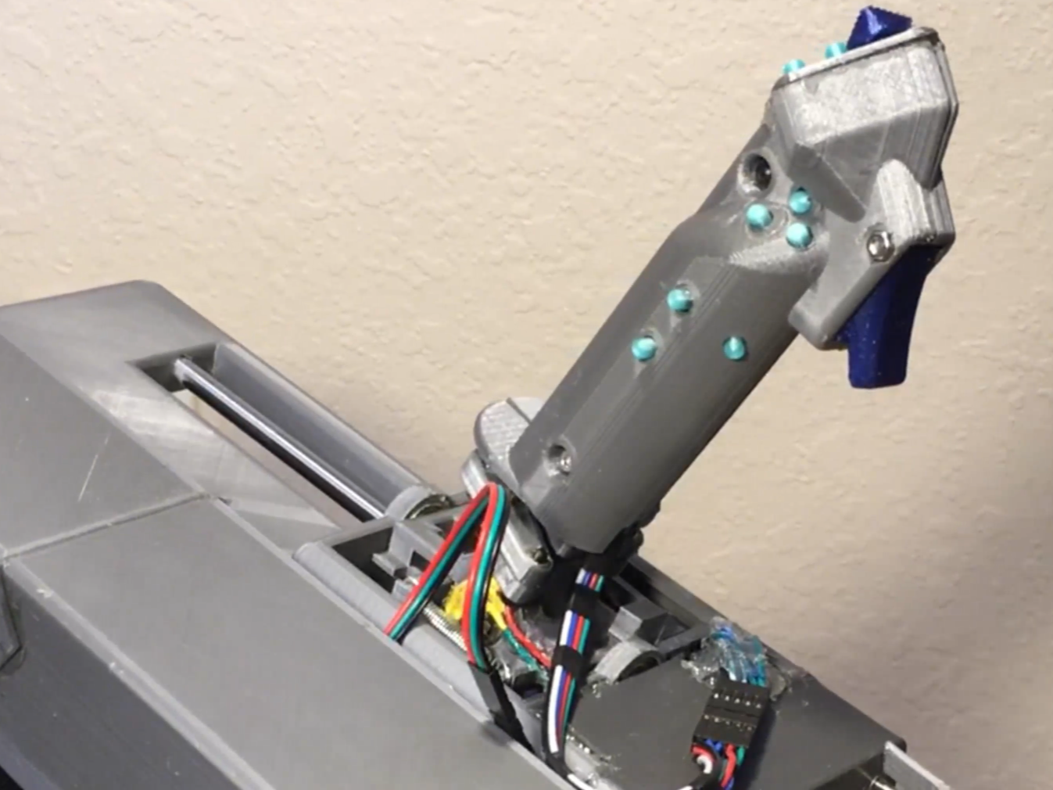
Images/Final Result/Throttle Joystick Side Videw.png
